ArgOsciProyect/ARG_OSCI_HARDWARE/Images/3D_Model_Argosci_PCB_and_case/Rear-Left_Isometric-Argosci_PCB_and_case.png

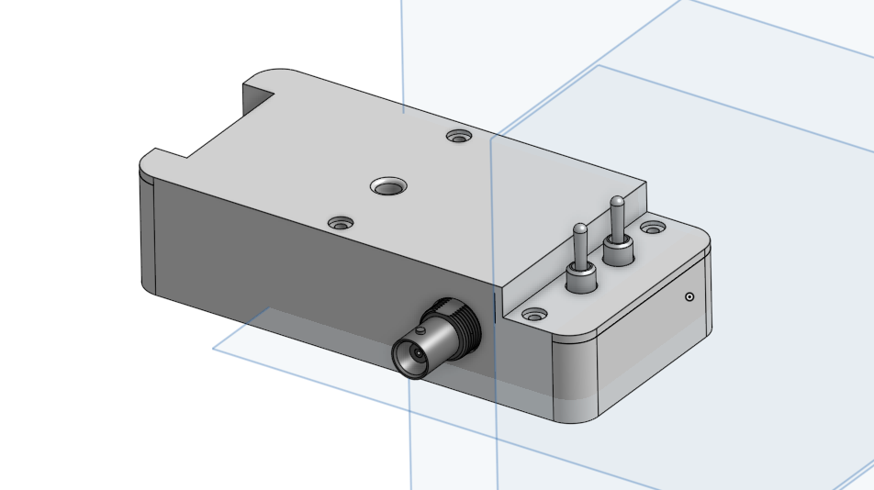
Images/3D_Model_Argosci_PCB_and_case/Rear-Left_Isometric-Argosci_PCB_and_case.png
