ArgOsciProyect/ARG_OSCI_HARDWARE/Images/3D_Model_Argosci_PCB_and_case/Top_Side-Argosci_PCB_and_case.png

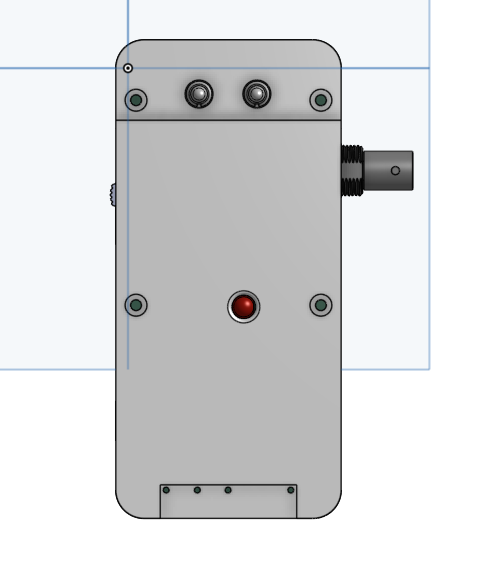
Images/3D_Model_Argosci_PCB_and_case/Top_Side-Argosci_PCB_and_case.png
