ArgOsciProyect/ARG_OSCI_HARDWARE/Images/Argosci_PCB/Bot_Side-Argosci_PCB.png

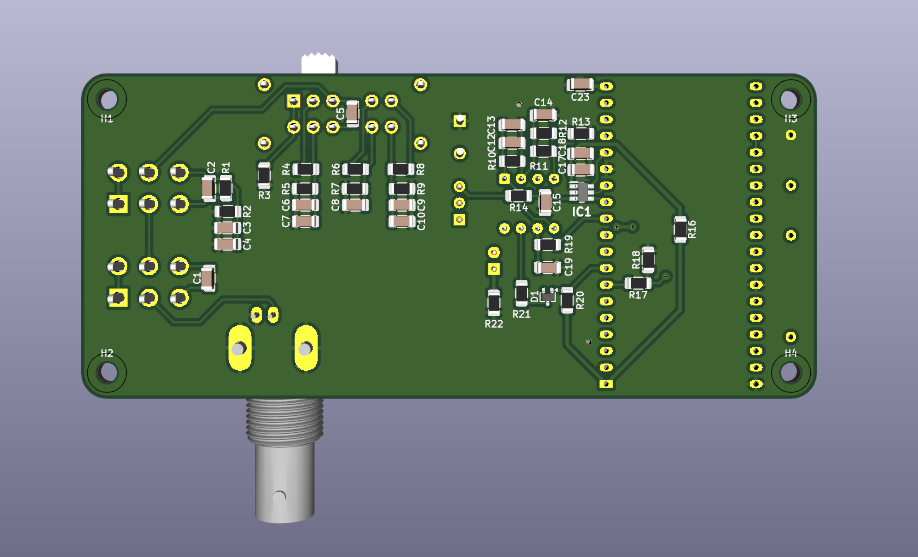
Images/Argosci_PCB/Bot_Side-Argosci_PCB.png
