ArgOsciProyect/ARG_OSCI_HARDWARE/Images/Argosci_PCB/Front-Right_Isometric-Argosci_PCB.png

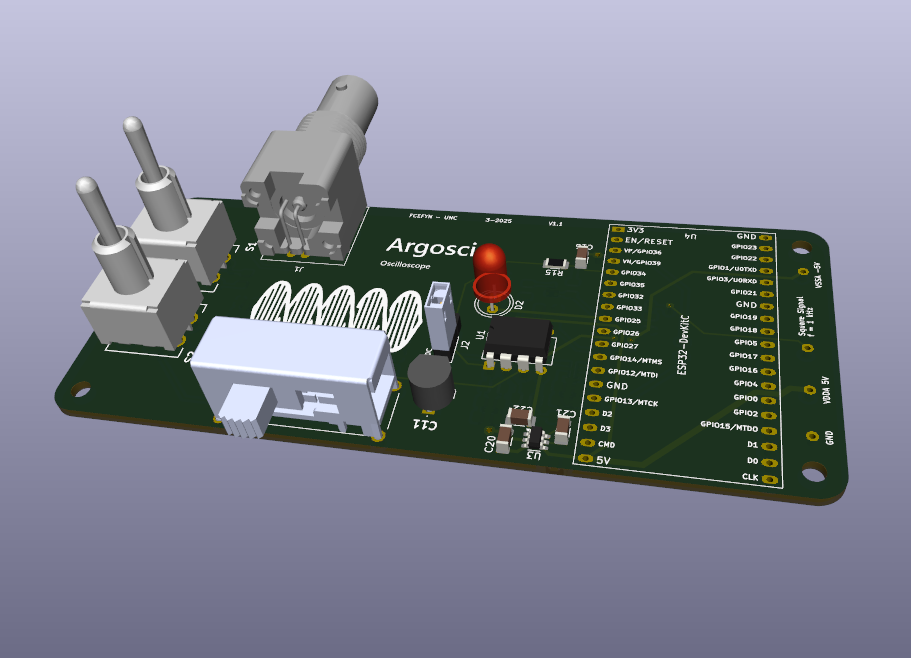
Images/Argosci_PCB/Front-Right_Isometric-Argosci_PCB.png
