ArgOsciProyect/ARG_OSCI_HARDWARE/Images/Argosci_PCB/Top_Side-Argosci_PCB.png

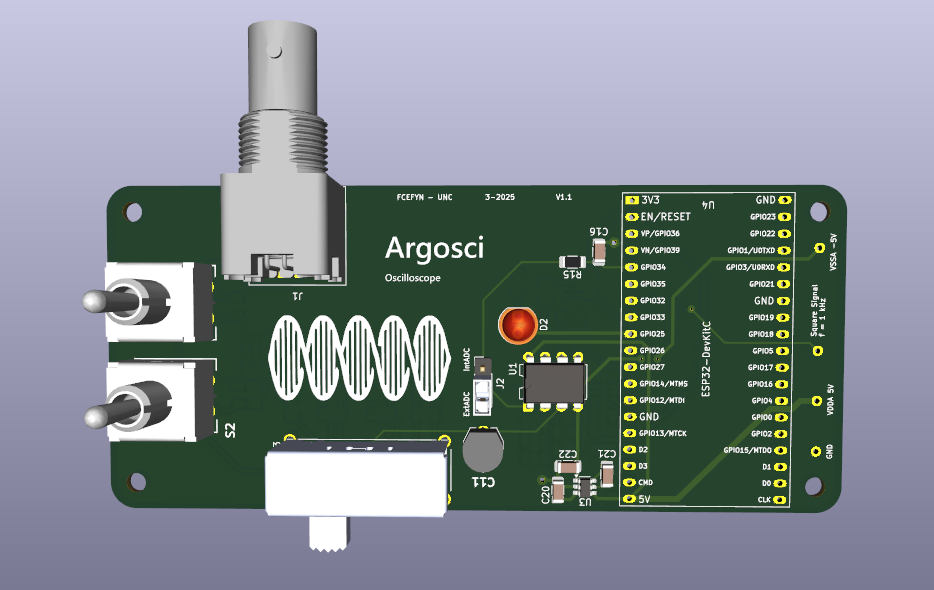
Images/Argosci_PCB/Top_Side-Argosci_PCB.png
