ArgOsciProyect/ARG_OSCI_HARDWARE/Images/PCB_layout/Bot_Side-PCB_layout.png

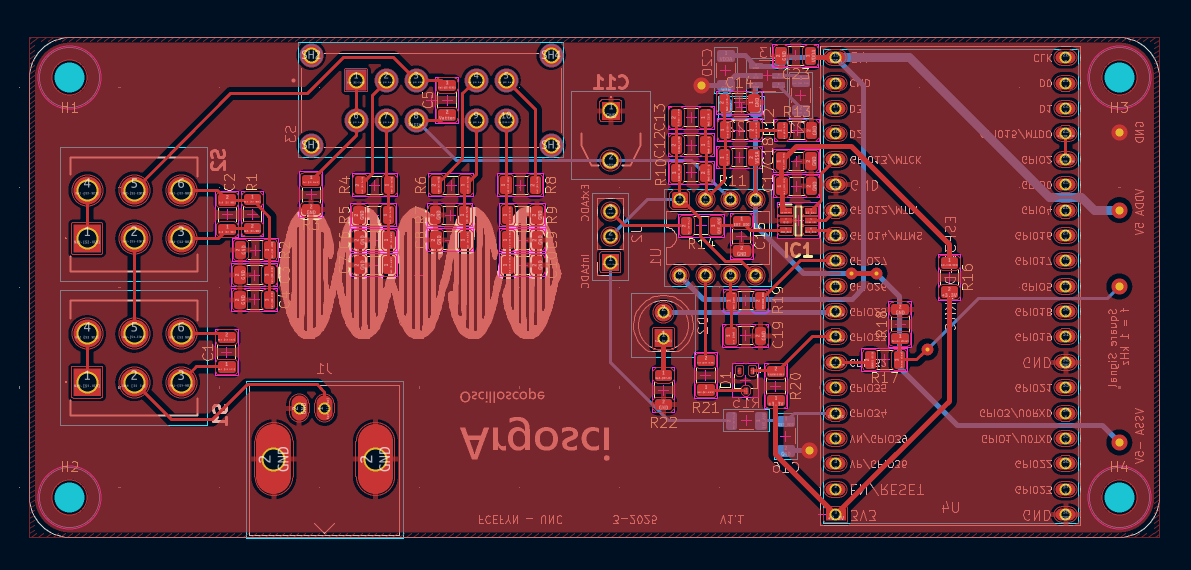
Images/PCB_layout/Bot_Side-PCB_layout.png
