ArgOsciProyect/ARG_OSCI_HARDWARE/Images/PCB_layout/PCB_snippets/ESP32_PCB_layout.jpg

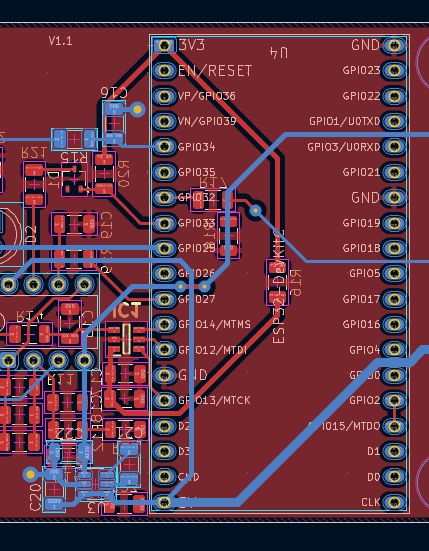
Images/PCB_layout/PCB_snippets/ESP32_PCB_layout.jpg
