ArgOsciProyect/ARG_OSCI_HARDWARE/Images/PCB_layout/Top_Side-PCB_layout.png

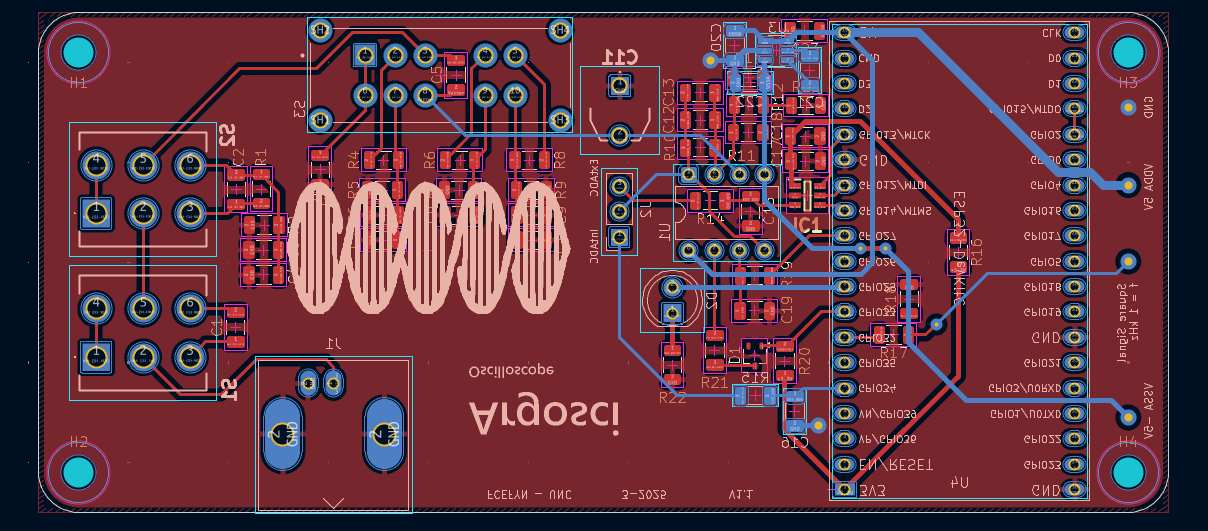
Images/PCB_layout/Top_Side-PCB_layout.png
