ArgOsciProyect/ARG_OSCI_HARDWARE/Images/Simplified_frequency_response_of_the_input_scales.jpg

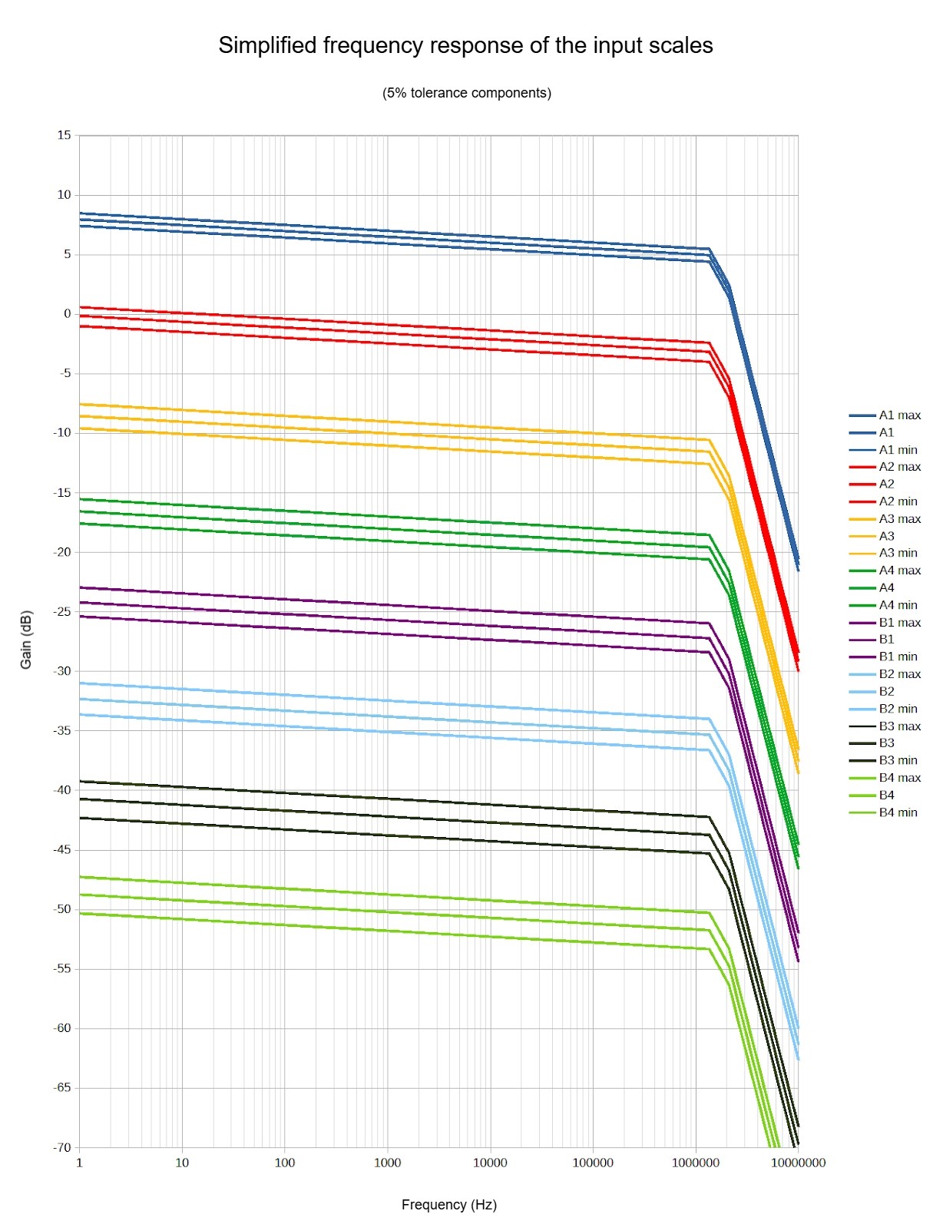
Images/Simplified_frequency_response_of_the_input_scales.jpg
